jorisvr/hw-sma-plug/sma2_plug_v2/pictures/assembled_board_connector.jpg

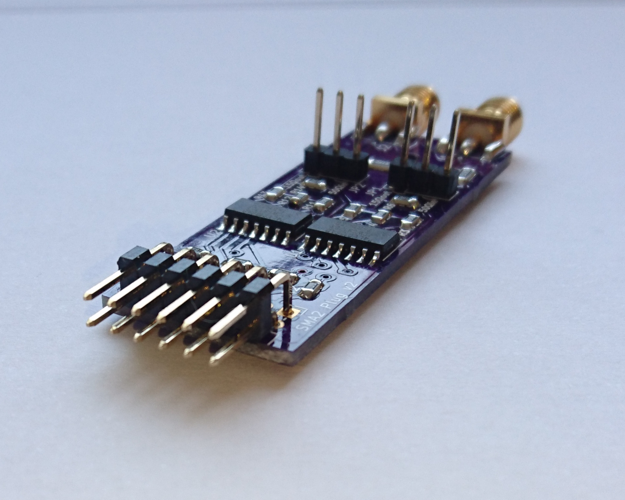
sma2_plug_v2/pictures/assembled_board_connector.jpg
